DanielCasner/LED-drivers/simulation/LT37561-2 boost.asc

C1: cap; 4.7µ; V=25
C2: cap; 4.7µ; Rser=3m
C3: cap; 1000p
C4: cap; .3µ
C5: cap; 4.7µ; V=25
C6: polcap; 220µ; V=25 Irms=555m Rser=0.13 Lser=0 mfg="United Chemi-Con" pn="LXF25VB221M8X15LL" type="Al electrolytic"
D1: schottky; PDS5100
D2: LED; NSCW100
D3: LED; NSCW100
D4: LED; NSCW100
D5: LED; NSCW100
D6: LED; NSCW100
D7: LED; NSCW100
D8: LED; NSCW100
D9: LED; NSCW100
D10: LED; NSCW100
D11: LED; NSCW100
D12: LED; NSCW100
D13: LED; NSCW100
D14: LED; NSCW100
D15: LED; NSCW100
D16: LED; NSCW100
D17: LED; NSCW100
D18: LED; NSCW100
D19: LED; NSCW100
D20: LED; NSCW100
D21: LED; NSCW100
D22: LED; NSCW100
D23: LED; NSCW100
D24: LED; NSCW100
D25: LED; NSCW100
L1: ind; 22µ; Rpar=2K
Q1: nmos; IRFR120Z
Q2: nmos; IRFR120Z
R1: res; .018
R2: res; 953k; tol=1
R3: res; 12.4k; tol=1
R4: res; 4; tol=1
R5: res; 953k; tol=1
R6: res; 201k; tol=1
R7: res; 28.7K
R8: res; 100k; tol=5
R9: res; 16.9K
R10: res; 100K
R11: res; 75k; tol=5
R12: res; 10k; tol=5
U1: LT3756-2
V1: voltage; 12; Rser=4
V2: voltage; PULSE(0 3.3 0 1u 1u 1ms 2ms)
Named nets: 0, IN, out, /OPENLED, PWMout, GATE
.tran 50m startup
NTC
