DanielCasner/LED-drivers/simulation/LT37561-2 buck.asc

C1: cap; 15µF; V=100
C3: cap; 15µF; V=100
C4: cap; 4.7µ; V=100
C6: cap; 4.7µ; V=25
C7: cap; .05µ
C8: cap; 1000p
D1: schottky; PDS5100
D2: LED; NSCW100
D3: LED; NSCW100
D4: LED; NSCW100
D5: LED; NSCW100
D6: LED; NSCW100
D7: LED; NSCW100
D8: LED; NSCW100
D9: LED; NSCW100
L1: ind; 33µ; Rpar=2K
M1: nmos; Si3440DV
M2: pmos; Si7469DP
Q1: npn
Q2: pnp; 2N5401
R1: res; .1; tol=1
R2: res; 1K
R3: res; 5; tol=1
R4: res; 1.5k; tol=5
R5: res; 953k; tol=1
R6: res; 201k; tol=1
R7: res; 28.7K
R8: res; 11k; tol=5
R9: res; 16.9K
R10: res; 100K
R11: res; 200K; tol=5
R12: res; 47k; tol=5
R13: res; 200K; tol=5
R14: res; 200K; tol=5
R15: res; 100k; tol=5
U1: LT3756-2
V1: voltage; 80; Rser=4
V2: voltage; PULSE(0 3.3 0 2u 2u .4m 1m)
V3: voltage; 3.3
Named nets: 0, IN, /OPENLED, PWMout, GATE
.tran 50m startup
NTC
